AlfredoSequeida/hello-world/models/e.stl

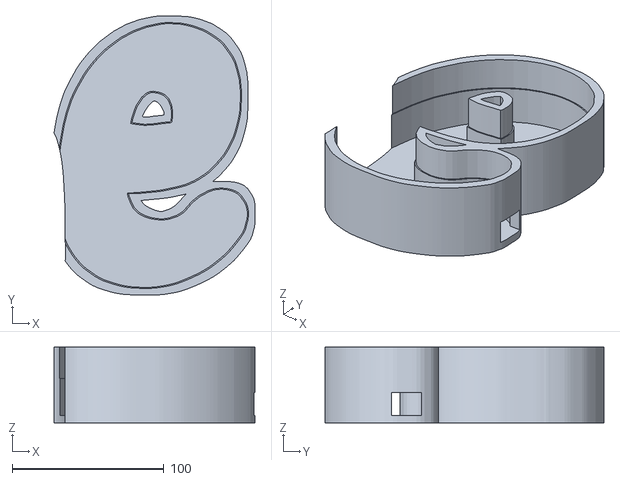
[picture p15: CAD file, 2021-02-09]
models/e.stl
132.7 x 184.1 x 50.0
