AlfredoSequeida/hello-world/models/h_insert.stl

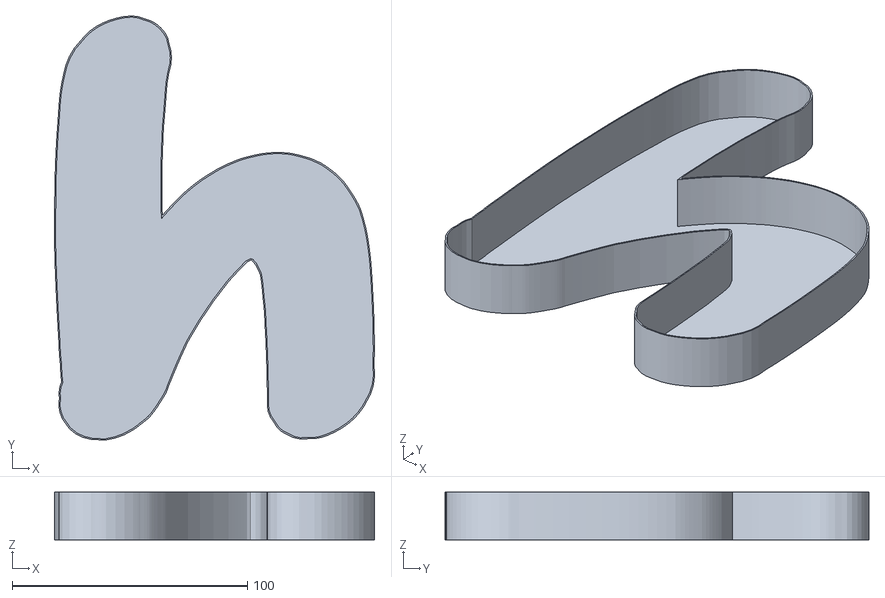
[picture p16: CAD file, 2021-02-09]
models/h_insert.stl
136.1 x 180.3 x 20.4
