AlfredoSequeida/hello-world/models/w_insert.stl

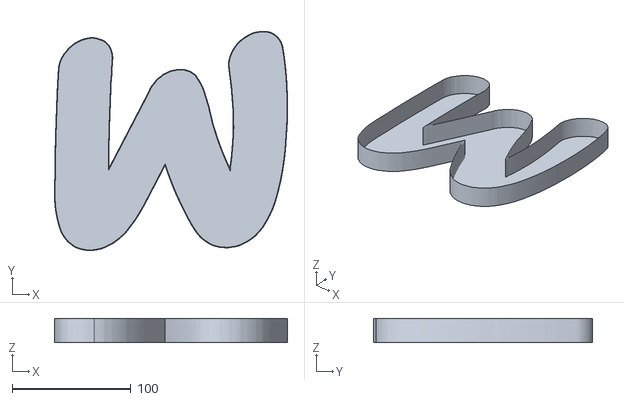
[picture p17: CAD file, 2021-02-09]
models/w_insert.stl
196.0 x 184.2 x 20.4
